bassistTech/ChannelTwoPreamp/Docs/imgv2/HPFcurve.png

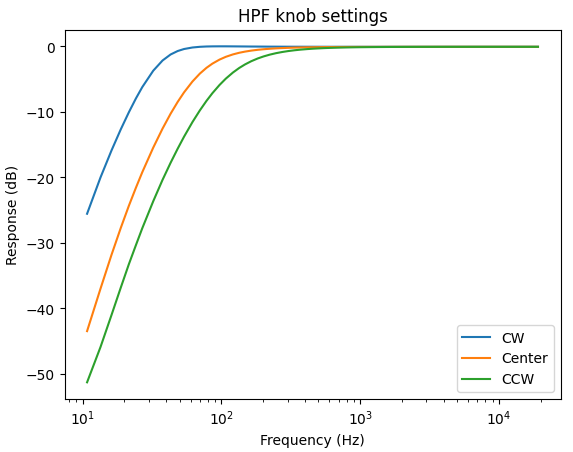
Docs/imgv2/HPFcurve.png
