bassistTech/ChannelTwoPreamp/Docs/imgv2/Mix.png

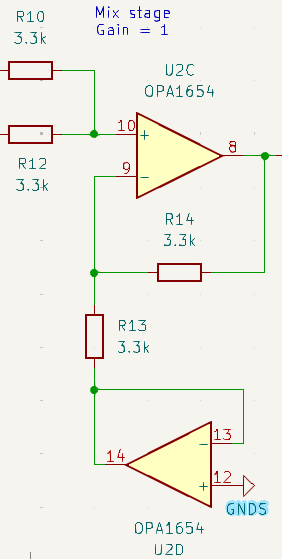
Docs/imgv2/Mix.png
