bassistTech/ChannelTwoPreamp/Docs/imgv2/PowerCircuit.png

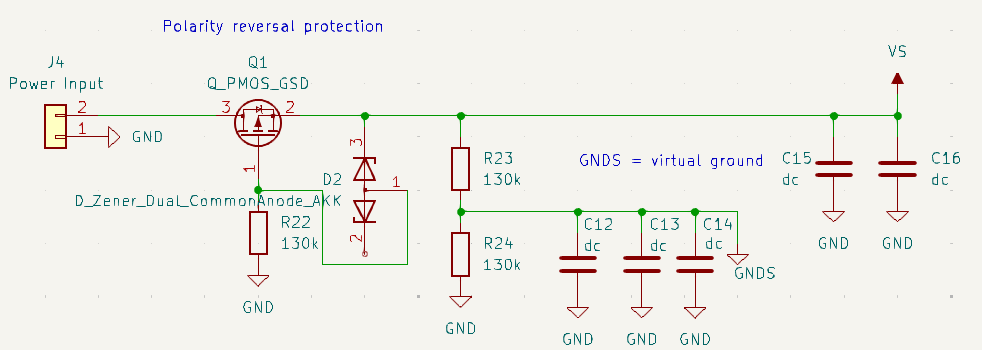
Docs/imgv2/PowerCircuit.png
