bassistTech/ChannelTwoPreamp/Docs/imgv2/tonecurve.png

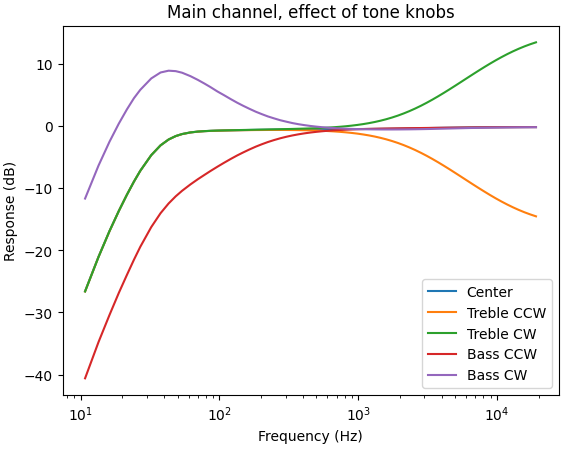
Docs/imgv2/tonecurve.png
