bassistTech/ChannelTwoPreamp/Docs/imgv2/UseNoJacks.png

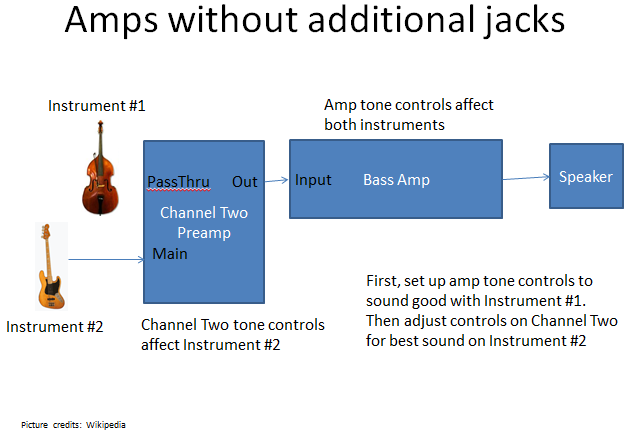
Docs/imgv2/UseNoJacks.png
