bassistTech/ChannelTwoPreamp/Modeling/Power circuit.png

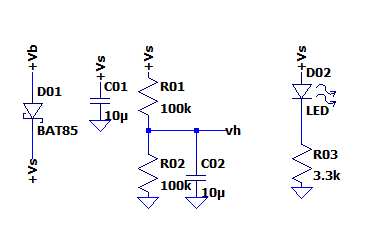
Modeling/Power circuit.png
