bassistTech/ChannelTwoPreamp/Docs/buildV1/build1.png

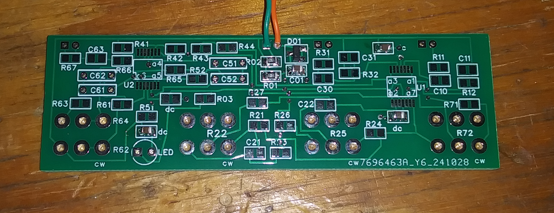
Docs/buildV1/build1.png
