bassistTech/ChannelTwoPreamp/Docs/buildV1/build2.png

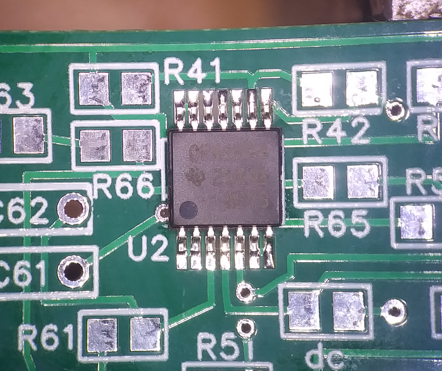
Docs/buildV1/build2.png
