bassistTech/ChannelTwoPreamp/Docs/buildV1/build4.png

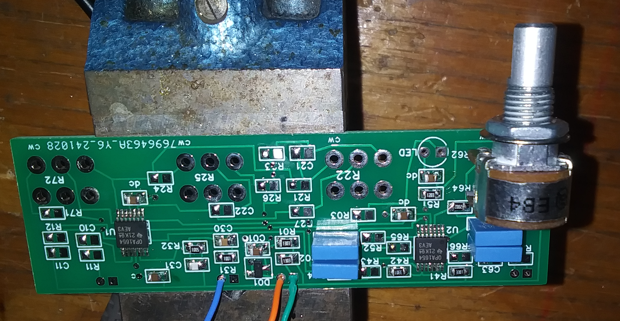
Docs/buildV1/build4.png
