bassistTech/ChannelTwoPreamp/Docs/buildV1/build7.png

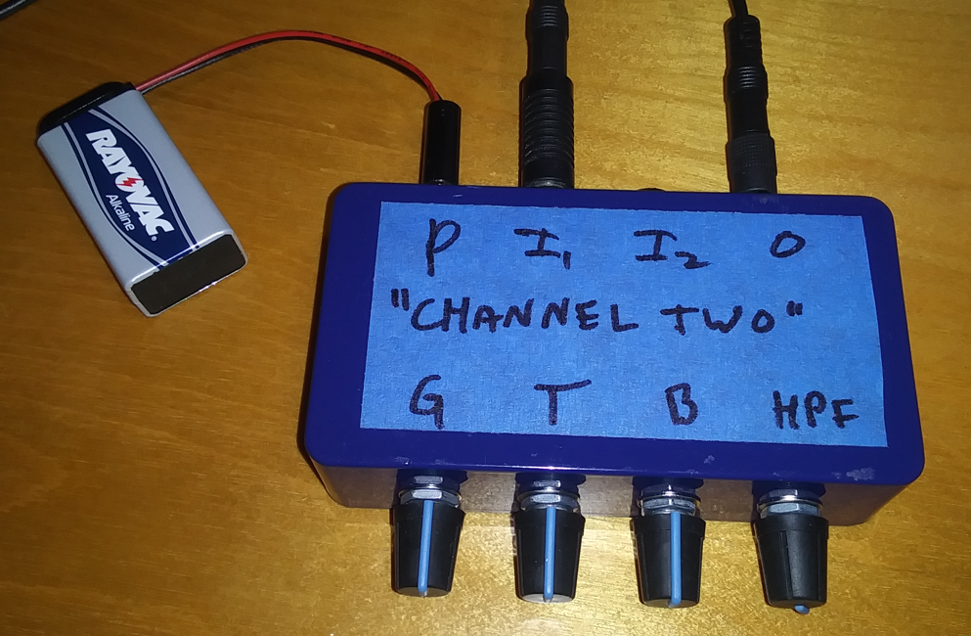
Docs/buildV1/build7.png
