bassistTech/ChannelTwoPreamp/Docs/buildV1/build8.png

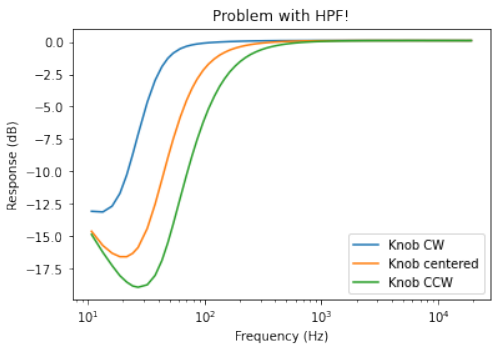
Docs/buildV1/build8.png
