bassistTech/ChannelTwoPreamp/Docs/imgv2/R41_fix.png

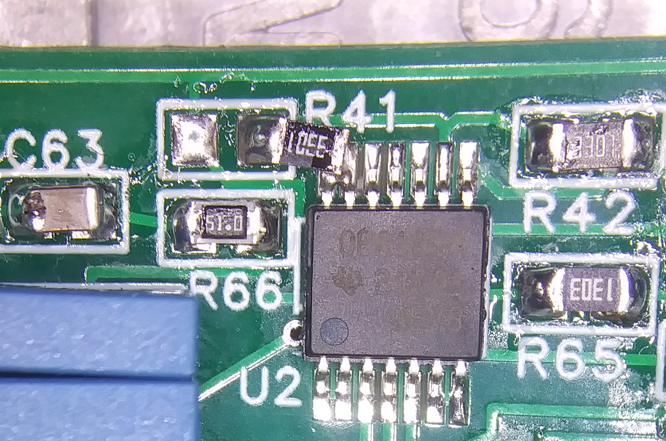
Docs/imgv2/R41_fix.png
