bassistTech/ChannelTwoPreamp/Schematic and Modeling/Channel Two model circuit v2.asc

A1: LTC6079
A2: LTC6079
A3: LTC6079
A4: LTC6079
A5: LTC6079
A6: LTC6079
A7: LTC6079
A8: LTC6079
C10: cap; 33n
C11: cap; 100p
C21: cap; 47n
C22: cap; 2.2n
C30: cap; 33n
C31: cap; 100p
C51: cap; 82n
C52: cap; 82n
C61: cap; 82n
C62: cap; 82n
C63: cap; 10µ
R11: res; 1k
R12: res; 10Meg
R21: res; 22k
R22a: res; 50k
R22b: res; 50k
R23: res; 22k
R24: res; 10k
R25a: res; 50k
R25b: res; 50k
R26: res; 10k
r27: res; 22k
R31: res; 1k
R32: res; 10Meg
R41: res; 3.3k
R42: res; 3.3k
R43: res; 3.3k
R44: res; 3.3k
R51: res; 120k
R52: res; 120k
R61: res; 20k
R62: POT; 100k
R63: res; 20k
R64: POT; 100k
R65: res; 150k
R66: res; 51
R67: res; 100k
R71: res; 1k
R72a: res; 4500
R72b: res; 5500
V1: voltage; SINE(0 0.1 1000); AC 1.
V2: voltage; 5
V3: voltage; 2.5
Named nets: 0, Main, +Vs, vh, PassThru, out
.ac oct 100 10 10000
cw
cw
R6a + R6b = dual ganged pot
HPF frequency control
Filter 1
Gain = 1
Filter 2
Gain = 1
Bass
100k linear taper
Treble
100k linear taper
cw
cw
ccw
ccw
Gain (Volume)
10k linear taper
cw
ccw
Unused op amp section
Gain = 1
Gain = 0 to 10
Gain = 1
With knobs centered
Gain = 0.5
Gain = 2
